Templatew/PolyBuzz/Rapports séances/CAZAUBON Lorenz/Séance 4/Bouton.ino

//#include <Wire.h>
//#include <LiquidCrystal_I2C.h>

//LiquidCrystal_I2C lcd(0x27, 20, 4);

// Bouton
int bouton_pins[] = {
  53, 51, 49
};


// LED
int led_pins[] = {
  52, 50, 48
};


// Liste bouton taille
const int NOMBRE_BOUTON = sizeof(bouton_pins)/sizeof(bouton_pins[0]); 

// Bouton random
int bouton_aleatoire = 0;
int led_eteinte = 1;

// Temps limite pression bouton (jeu_deux)
unsigned long temps_ini = 0;
unsigned long intervalle = 2000;

// Choix du jeu
int choix_jeu = 2;

// Simon liste bouton
int temps_simon = 500;
int counter = 0;
int num_courant = 0;
String str_num_courant = "";
String etat = "simon";
String liste_simon = "";
String liste_simon_joueur = "";

// Score
int score = 0;

void pinMode_bouton() {
  
  // Initialiser les pins boutons
  for (int i = 0; i < NOMBRE_BOUTON; i++) { 
    pinMode(bouton_pins[i], INPUT_PULLUP);
  }
  Serial.println("Bouton ok");
}

void pinMode_led() {
  
  // Initialiser les pins LED
  for (int i = 0; i < NOMBRE_BOUTON; i++) { 
    pinMode(led_pins[i], OUTPUT);
  }
  Serial.println("LED ok");
}

void LED_off() {
  for (int i = 0; i <= 10; i++) { 
    digitalWrite(led_pins[i], 1);
  }
}

void setup() {
    Serial.begin(9600);
    //lcd.init();
    pinMode_bouton();
    pinMode_led();
    LED_off(); 
}

void jeu_un_next() {
  led_eteinte = 1;
  digitalWrite(bouton_aleatoire - 1, led_eteinte);
  bouton_aleatoire = bouton_pins[random(0,NOMBRE_BOUTON)];
  delay(200);
}

void jeu_un() {
  
  if ((bouton_aleatoire == 0) && (led_eteinte == 1)) {
    bouton_aleatoire = bouton_pins[random(0,NOMBRE_BOUTON)];
  }
  
  if (led_eteinte == 1) {
    led_eteinte = 0;
    digitalWrite(bouton_aleatoire - 1, led_eteinte);
    Serial.println(score);
  }
  
  if (led_eteinte == 0) {

    if ((choix_jeu == 1) && (millis() - temps_ini > intervalle)) {
        jeu_un_next();
        temps_ini += intervalle;
    }
    
    for (int i = 0; i < NOMBRE_BOUTON; i++) {

      if (digitalRead(bouton_pins[i]) == 0) {
        if (bouton_pins[i] != bouton_aleatoire) {
          if (score>0) {score -= 1;}
        }
        else {score += 1;}
        jeu_un_next();
        Serial.println(score);
        
      }
    }  
  }
}

void simon() {
    // V1
    if (etat == "simon") {
      liste_simon += random(0,NOMBRE_BOUTON);
      Serial.println("Simon "+liste_simon);
      for (int i = 0; i < liste_simon.length(); i++) {
        str_num_courant = liste_simon[i];
        num_courant = str_num_courant.toInt();
        digitalWrite(led_pins[num_courant],0);
        delay(temps_simon);
        LED_off();
        delay(temps_simon);
      }
      etat = "joueur";
    }

    if (etat == "joueur") {
      for (int i = 0; i < NOMBRE_BOUTON; i++) {
        if (digitalRead(bouton_pins[i]) == 0) {
          liste_simon_joueur += i;
          Serial.println("Joueur " + liste_simon_joueur);
          delay(200);
        }
      }
      //?
      if ((liste_simon_joueur.length() >= 1) || (liste_simon_joueur[-1] != liste_simon[liste_simon_joueur.length() - 1])) {
        etat == "stop";
      }

      if ( (liste_simon_joueur.length() == liste_simon.length()) || (liste_simon_joueur == liste_simon)) {
        etat = "simon";
        liste_simon_joueur = "";
        delay(800);
      }
      
    }
}

void afficher_score() {
  //lcd.backlight();
  // Envoi du message
  //lcd.setCursor(0, 0);
  //lcd.print("SCORE: ");
  //lcd.setCursor(7, 0);
  //lcd.print(score);
}


void loop() {
  
  //afficher_score();
  if ((choix_jeu==0) || (choix_jeu == 1)) {
    jeu_un();
     
    
  }
  else if (choix_jeu == 2) {
    simon();
  }
    
}
